jbilander/AmigaPSU_Enclosure_for_XP_Power_ECM60UT31/images/AmigaPSU_Enclosure_for_XP_Power_ECM60UT31_pic54.jpg

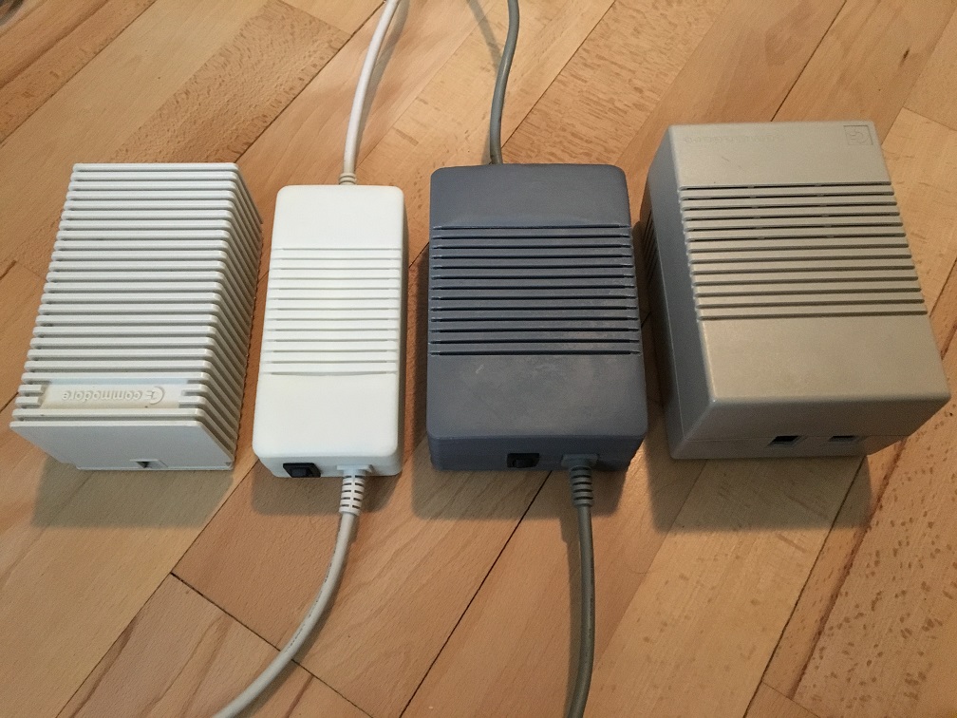
images/AmigaPSU_Enclosure_for_XP_Power_ECM60UT31_pic54.jpg
